BPera1111/Proyecto_Micro/CNC/Core/Src/motion.c

/*
  motion.c - Implementación del módulo de control de movimiento para CNC Controller
  
  Este archivo contiene todas las funciones relacionadas con el movimiento
  de los motores paso a paso y control de ejes.
*/

#include <stdlib.h>   // Para abs()
#include <stdio.h>    // Para snprintf(), sscanf(), printf()
#include <string.h>   // Para memset(), strncmp(), strcpy(), strlen()
#include <stdint.h>   // Para uint32_t
#include <stdbool.h>  // Para bool
#include <math.h>     // Para funciones matemáticas
#include "stm32f1xx_hal.h"  // Para HAL functions
#include "main.h"
#include "config.h"
#include "motion.h"


// ===========================================================================================

// VARIABLES GLOBALES DE POSICIÓN (declaradas como extern - definidas en main.c)
// ===========================================================================================

// Variables de posición actual en pasos (definidas en main.c)
extern int32_t currentX, currentY, currentZ;

// Variables de velocidad (definidas en main.c)
extern float currentFeedRate;
extern float rapidRate;
extern float maxFeedRate;
extern char gcodeProgram[MAX_GCODE_LINES][MAX_LINE_LENGTH];

// ===========================================================================================
// FUNCIONES AUXILIARES PRIVADAS
// ===========================================================================================

/**
  * @brief  Función de delay de microsegundos usando DWT
  * @param  us: Cantidad de microsegundos a esperar
  * @retval None
  */
void delay_us(uint32_t us) {
    uint32_t cycles = (SystemCoreClock / 1000000L) * us;
    uint32_t start = DWT->CYCCNT;
    while ((DWT->CYCCNT - start) < cycles);
}

/**
  * @brief  Calcula el delay entre "ticks" del interpolador según feed y distancia
  * @param  feedRate_mm_min: Velocidad en mm/min (G0/G1)
  * @param  total_distance_mm: Distancia del segmento en mm
  * @param  maxSteps: Máximo de pasos entre ejes (Bresenham base)
  * @retval Delay en microsegundos entre ticks
  */
uint32_t calculateStepDelay(float feedRate_mm_min, float total_distance_mm, int32_t maxSteps) {
    if (feedRate_mm_min <= 0.0f || total_distance_mm <= 0.0f || maxSteps <= 0) {
        return STEP_DELAY_US;  // fallback
    }

    // mm/min -> mm/s
    float v_mm_s = feedRate_mm_min;

    // Tiempo total para recorrer el segmento a ese feed
    float total_time_s = total_distance_mm / v_mm_s;   // s

    // Tiempo entre "ticks" (cada tick puede disparar 0..3 pasos según Bresenham)
    float t_step_s = total_time_s / (float)maxSteps;   // s/tick

    // Convertir a microsegundos
    uint32_t delay_us = (uint32_t)(t_step_s * 1000000.0f);

    // Limitar si querés un mínimo por hardware/temporizador
    if (delay_us < 200) delay_us = 200;

    return delay_us;
}

// ===========================================================================================
// FUNCIONES DE MOVIMIENTO BÁSICO POR PASOS
// ===========================================================================================

/**
  * @brief  Ejecuta un solo paso en el eje X
  * @retval None
  */
void X_stepOnce(void) {
    HAL_GPIO_WritePin(GPIOB, X_STEP_PIN, GPIO_PIN_SET);
    delay_us(2);
    HAL_GPIO_WritePin(GPIOB, X_STEP_PIN, GPIO_PIN_RESET);
}

/**
  * @brief  Ejecuta un solo paso en el eje Y
  * @retval None
  */
void Y_stepOnce(void) {
    HAL_GPIO_WritePin(GPIOB, Y_STEP_PIN, GPIO_PIN_SET);
    delay_us(2);
    HAL_GPIO_WritePin(GPIOB, Y_STEP_PIN, GPIO_PIN_RESET);
}

/**
  * @brief  Ejecuta un solo paso en el eje Z
  * @retval None
  */
void Z_stepOnce(void) {
    HAL_GPIO_WritePin(GPIOA, Z_STEP_PIN, GPIO_PIN_SET);
    delay_us(2);
    HAL_GPIO_WritePin(GPIOA, Z_STEP_PIN, GPIO_PIN_RESET);
}

/**
  * @brief  Mueve el eje X una cantidad específica de pasos
  * @param  steps: Número de pasos a mover
  * @param  dir: Dirección del movimiento (true = positivo, false = negativo)
  * @retval None
  */
void X_move(int32_t steps, bool dir) {
    // Configura dirección
    HAL_GPIO_WritePin(GPIOB, X_DIR_PIN, dir ? GPIO_PIN_SET : GPIO_PIN_RESET);

    // Ejecuta los pasos
    for (int32_t i = 0; i < steps; i++) {
        X_stepOnce();
        delay_us(STEP_DELAY_US);
    }
}

/**
  * @brief  Mueve el eje Y una cantidad específica de pasos
  * @param  steps: Número de pasos a mover
  * @param  dir: Dirección del movimiento (true = positivo, false = negativo)
  * @retval None
  */
void Y_move(int32_t steps, bool dir) {
    // Configura dirección
    HAL_GPIO_WritePin(GPIOB, Y_DIR_PIN, dir ? GPIO_PIN_SET : GPIO_PIN_RESET);
    // Ejecuta los pasos
    for (int32_t i = 0; i < steps; i++) {
        Y_stepOnce();
        delay_us(STEP_DELAY_US);
    }
}

/**
  * @brief  Mueve el eje Z una cantidad específica de pasos
  * @param  steps: Número de pasos a mover
  * @param  dir: Dirección del movimiento (true = positivo, false = negativo)
  * @retval None
  */
void Z_move(int32_t steps, bool dir) {
    // Configura dirección
    HAL_GPIO_WritePin(GPIOA, Z_DIR_PIN, dir ? GPIO_PIN_RESET : GPIO_PIN_SET);
    // Ejecuta los pasos
    for (int32_t i = 0; i < steps; i++) {
        Z_stepOnce();
        delay_us(STEP_DELAY_US);
    }
}

// ===========================================================================================
// FUNCIONES DE CONTROL DE MOTORES
// ===========================================================================================

/**
  * @brief  Habilita todos los motores paso a paso
  * @retval None
  */
void enableSteppers(void) {
    // Habilitar drivers (EN LOW = habilitado para la mayoría de drivers A4988/DRV8825)
    HAL_GPIO_WritePin(GPIOB, X_EN_PIN, GPIO_PIN_RESET);  // Enable motor X
    HAL_GPIO_WritePin(GPIOB, Y_EN_PIN, GPIO_PIN_RESET);  // Enable motor Y
    HAL_GPIO_WritePin(GPIOA, Z_EN_PIN, GPIO_PIN_RESET);  // Enable motor Z
}

/**
  * @brief  Deshabilita todos los motores paso a paso
  * @retval None
  */
void disableSteppers(void) {
    // Deshabilitar drivers (EN HIGH = deshabilitado para la mayoría de drivers A4988/DRV8825)
    HAL_GPIO_WritePin(GPIOB, X_EN_PIN, GPIO_PIN_SET);    // Disable motor X
    HAL_GPIO_WritePin(GPIOB, Y_EN_PIN, GPIO_PIN_SET);    // Disable motor Y
    HAL_GPIO_WritePin(GPIOA, Z_EN_PIN, GPIO_PIN_SET);    // Disable motor Z
}

// ===========================================================================================
// FUNCIONES DE MOVIMIENTO COORDINADO
// ===========================================================================================

/**
  * @brief  Movimiento de ejes con control de feed rate (versión avanzada)
  * @param  x, y, z: Coordenadas objetivo en mm
  * @param  feedRate: Velocidad en mm/min
  * @param  isRapid: true para G0 (rapid), false para G1 (linear)
  * @retval None
  */
void moveAxesWithFeedRate(float x, float y, float z, float feedRate, bool isRapid) {
    // Calcular posiciones objetivo en pasos
    int32_t targetX = !isnan(x) ? (int32_t)(x * STEPS_PER_MM_X) : currentX;
    int32_t targetY = !isnan(y) ? (int32_t)(y * STEPS_PER_MM_Y) : currentY;
    int32_t targetZ = !isnan(z) ? (int32_t)(z * STEPS_PER_MM_Z) : currentZ;
    
    // Calcular diferencias (pasos relativos)
    int32_t deltaX = targetX - currentX;
    int32_t deltaY = targetY - currentY;
    int32_t deltaZ = targetZ - currentZ;
    
    // Calcular distancia total en mm para determinar velocidad
    float distance_X = !isnan(x) ? fabs(x - (currentX / (float)STEPS_PER_MM_X)) : 0;
    float distance_Y = !isnan(y) ? fabs(y - (currentY / (float)STEPS_PER_MM_Y)) : 0;
    float distance_Z = !isnan(z) ? fabs(z - (currentZ / (float)STEPS_PER_MM_Z)) : 0;
    float total_distance = sqrt(distance_X*distance_X + distance_Y*distance_Y + distance_Z*distance_Z);
    
    // Seleccionar velocidad según el tipo de movimiento
    float effective_feedrate = isRapid ? rapidRate : feedRate;


    
    // Limitar velocidad máxima
    if (effective_feedrate > maxFeedRate) {
        effective_feedrate = maxFeedRate;
    }
    
    // Determinar direcciones
    bool dirX = (deltaX >= 0);
    bool dirY = (deltaY >= 0);
    bool dirZ = (deltaZ >= 0);
    
    // Configurar direcciones de los motores
    if (deltaX != 0) HAL_GPIO_WritePin(GPIOB, X_DIR_PIN, dirX ? GPIO_PIN_SET : GPIO_PIN_RESET);
    if (deltaY != 0) HAL_GPIO_WritePin(GPIOB, Y_DIR_PIN, dirY ? GPIO_PIN_SET : GPIO_PIN_RESET);
    if (deltaZ != 0) HAL_GPIO_WritePin(GPIOA, Z_DIR_PIN, dirZ ? GPIO_PIN_RESET : GPIO_PIN_SET);
    
    // Convertir a valores absolutos para el algoritmo
    deltaX = (deltaX < 0) ? -deltaX : deltaX;
    deltaY = (deltaY < 0) ? -deltaY : deltaY;
    deltaZ = (deltaZ < 0) ? -deltaZ : deltaZ;

        // Algoritmo de interpolación lineal 3D (Bresenham modificado)
    int32_t maxSteps = deltaX;
    if (deltaY > maxSteps) maxSteps = deltaY;
    if (deltaZ > maxSteps) maxSteps = deltaZ;
    
    if (maxSteps == 0) return; // No hay movimiento
    
    // Calcular delay basado en feed rate
    uint32_t step_delay = calculateStepDelay(effective_feedrate, total_distance, maxSteps);
    
    // Mostrar información del movimiento con validación de valores
    // float display_x = !isnan(x) ? x : (currentX / (float)STEPS_PER_MM_X);
    // float display_y = !isnan(y) ? y : (currentY / (float)STEPS_PER_MM_Y);
    // float display_z = !isnan(z) ? z : (currentZ / (float)STEPS_PER_MM_Z);
    
    // Convertir floats a enteros para evitar problemas de printf con floats
    // int x_int = (int)display_x;
    // int x_dec = (int)((display_x - x_int) * 100);
    // int y_int = (int)display_y;
    // int y_dec = (int)((display_y - y_int) * 100);
    // int z_int = (int)display_z;
    // int z_dec = (int)((display_z - z_int) * 100);
    // int f_int = (int)effective_feedrate;
    // int f_dec = (int)((effective_feedrate - f_int) * 10);
    // int d_int = (int)total_distance;
    // int d_dec = (int)((total_distance - d_int) * 100);

    // snprintf(outputBuffer, OUTPUT_BUFFER_SIZE, "%s: X=%d.%02d Y=%d.%02d Z=%d.%02d F=%d.%d D=%d.%02dmm T=%lduS\r\n", 
    //        isRapid ? "G0 RAPID" : "G1 LINEAR",
    //        x_int, abs(x_dec),
    //        y_int, abs(y_dec), 
    //        z_int, abs(z_dec),
    //        f_int, abs(f_dec), 
    //        d_int, abs(d_dec), 
    //        (unsigned long)step_delay);
    // sendUSBText(outputBuffer);
    // memset(outputBuffer, 0, OUTPUT_BUFFER_SIZE);
    
    
    // Variables para el algoritmo de Bresenham 3D
    int32_t errorX = maxSteps / 2;
    int32_t errorY = maxSteps / 2;
    int32_t errorZ = maxSteps / 2;
    
    // // Actualizar posiciones actuales
    // currentX = targetX;
    // currentY = targetY;
    // currentZ = targetZ;

    // Ejecutar pasos interpolados con feed rate controlado
    for (int32_t step = 0; step < maxSteps; step++) {
    bool stepX = false, stepY = false, stepZ = false;

    errorX += deltaX; if (errorX >= maxSteps) { errorX -= maxSteps; stepX = true; }
    errorY += deltaY; if (errorY >= maxSteps) { errorY -= maxSteps; stepY = true; }
    errorZ += deltaZ; if (errorZ >= maxSteps) { errorZ -= maxSteps; stepZ = true; }

    if (stepX){
      X_stepOnce();
      currentX += (dirX ? 1 : -1);
    }
    if (stepY){
      Y_stepOnce();
      currentY += (dirY ? 1 : -1);
    }
    if (stepZ){
      Z_stepOnce();
      currentZ += (dirZ ? 1 : -1);
    }

    delay_us(step_delay);
}
    
    

}

// ===========================================================================================
// FUNCIONES DE MOVIMIENTO DE ARCOS
// ===========================================================================================

/**
  * @brief  Movimiento de arco con radio específico
  * @param  x_end, y_end: Coordenadas finales del arco en mm
  * @param  r: Radio del arco en mm
  * @param  clockwise: Dirección del arco (1 = horario, 0 = antihorario)
  * @param  feedRate: Velocidad de alimentación en mm/s
  * @retval None
  */
void arc_move_r(float x_end, float y_end, float r, bool clockwise, float feedRate) {
    float x0 = currentX;
    float y0 = currentY;
    float x1 = x_end * STEPS_PER_MM_X;
    float y1 = y_end * STEPS_PER_MM_Y;
    r = r * STEPS_PER_MM_X; // Convertir radio a pasos

    float dx = x1 - x0;
    float dy = y1 - y0;
    float d = sqrt(dx * dx + dy * dy);

    if (d > 2 * fabs(r)) {
        sendUSBText("Error: el radio es muy pequeño para unir los puntos.\r\n");
        return;
    }

    // Punto medio entre inicio y fin
    float mx = (x0 + x1) / 2;
    float my = (y0 + y1) / 2;

    // Altura desde el punto medio al centro
    float h = sqrt(r * r - (d / 2) * (d / 2));

    // Vector perpendicular normalizado
    float nx = -dy / d;
    float ny = dx / d;

    // Determinar centro en una de las dos direcciones posibles
    float cx, cy;

    if (clockwise) {
        cx = mx - nx * h;
        cy = my - ny * h;
    } else {
        cx = mx + nx * h;
        cy = my + ny * h;
    }

    // Ángulos
    float start_angle = atan2(y0 - cy, x0 - cx);
    float end_angle = atan2(y1 - cy, x1 - cx);
    float total_angle = end_angle - start_angle;

    if (clockwise && total_angle > 0) {
        total_angle -= 2 * PI;
    } else if (!clockwise && total_angle < 0) {
        total_angle += 2 * PI;
    }

    for (int i = 1; i <= SEGMENTS; i++) {
        float angle = start_angle + total_angle * ((float)i / SEGMENTS);
        float x = cx + r * cos(angle);
        float y = cy + r * sin(angle);
        moveAxesWithFeedRate(x / STEPS_PER_MM_X, y / STEPS_PER_MM_Y, currentZ / STEPS_PER_MM_Z, feedRate, false);
    }
}

// ===========================================================================================
// FUNCIONES DE UTILIDAD
// ===========================================================================================

/**
  * @brief  Obtener posición actual en milímetros
  * @param  x, y, z: Punteros para almacenar las coordenadas actuales
  * @retval None
  */
void getCurrentPositionMM(float *x, float *y, float *z) {
    if (x) *x = currentX / (float)STEPS_PER_MM_X;
    if (y) *y = currentY / (float)STEPS_PER_MM_Y;
    if (z) *z = currentZ / (float)STEPS_PER_MM_Z;
}

/**
  * @brief  Establecer posición actual en pasos
  * @param  x_steps, y_steps, z_steps: Nueva posición en pasos
  * @retval None
  */
void setCurrentPosition(int32_t x_steps, int32_t y_steps, int32_t z_steps) {
    currentX = x_steps;
    currentY = y_steps;
    currentZ = z_steps;
}

/**
  * @brief  Establecer posición actual en milímetros
  * @param  x_mm, y_mm, z_mm: Nueva posición en milímetros
  * @retval None
  */
void setCurrentPositionMM(float x_mm, float y_mm, float z_mm) {
    currentX = (int32_t)(x_mm * STEPS_PER_MM_X);
    currentY = (int32_t)(y_mm * STEPS_PER_MM_Y);
    currentZ = (int32_t)(z_mm * STEPS_PER_MM_Z);
}
